rebecatourinho/opencimatec/vibrometro.X/sdcard.h

/* 
 * File:   sdcard.h
 * Author: rebecatourinho
 *
 * Created on March 24, 2014, 10:33 AM
 */

#ifndef SDCARD_H
#define	SDCARD_H

#ifdef	__cplusplus
extern "C" {
#endif




#ifdef	__cplusplus
}
#endif

#endif	/* SDCARD_H */
